sektor05/smartSwither/firmware/stm32cube/smartSwitcher/Core/Src/tim.c

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
/* Includes ------------------------------------------------------------------*/
#include "tim.h"

TIM_HandleTypeDef htim1;
TIM_HandleTypeDef htim2;
TIM_HandleTypeDef htim3;
TIM_HandleTypeDef htim4;

/* TIM1 init function */
void MX_TIM1_Init(void)
{

  TIM_ClockConfigTypeDef sClockSourceConfig = {0};
  TIM_MasterConfigTypeDef sMasterConfig = {0};

  htim1.Instance = TIM1;
  htim1.Init.Prescaler = 9;
  htim1.Init.CounterMode = TIM_COUNTERMODE_UP;
  htim1.Init.Period = 39;
  htim1.Init.ClockDivision = TIM_CLOCKDIVISION_DIV1;
  htim1.Init.RepetitionCounter = 0;
  htim1.Init.AutoReloadPreload = TIM_AUTORELOAD_PRELOAD_DISABLE;
  if (HAL_TIM_Base_Init(&htim1) != HAL_OK)
  {
    Error_Handler();
  }
  sClockSourceConfig.ClockSource = TIM_CLOCKSOURCE_INTERNAL;
  if (HAL_TIM_ConfigClockSource(&htim1, &sClockSourceConfig) != HAL_OK)
  {
    Error_Handler();
  }
  sMasterConfig.MasterOutputTrigger = TIM_TRGO_RESET;
  sMasterConfig.MasterSlaveMode = TIM_MASTERSLAVEMODE_DISABLE;
  if (HAL_TIMEx_MasterConfigSynchronization(&htim1, &sMasterConfig) != HAL_OK)
  {
    Error_Handler();
  }
}
/* TIM2 init function */
void MX_TIM2_Init(void)
{

  TIM_ClockConfigTypeDef sClockSourceConfig = {0};
  TIM_MasterConfigTypeDef sMasterConfig = {0};

  htim2.Instance = TIM2;
  htim2.Init.Prescaler = 9999;
  htim2.Init.CounterMode = TIM_COUNTERMODE_UP;
  htim2.Init.Period = 999;
  htim2.Init.ClockDivision = TIM_CLOCKDIVISION_DIV1;
  htim2.Init.AutoReloadPreload = TIM_AUTORELOAD_PRELOAD_DISABLE;
  if (HAL_TIM_Base_Init(&htim2) != HAL_OK)
  {
    Error_Handler();
  }
  sClockSourceConfig.ClockSource = TIM_CLOCKSOURCE_INTERNAL;
  if (HAL_TIM_ConfigClockSource(&htim2, &sClockSourceConfig) != HAL_OK)
  {
    Error_Handler();
  }
  sMasterConfig.MasterOutputTrigger = TIM_TRGO_RESET;
  sMasterConfig.MasterSlaveMode = TIM_MASTERSLAVEMODE_DISABLE;
  if (HAL_TIMEx_MasterConfigSynchronization(&htim2, &sMasterConfig) != HAL_OK)
  {
    Error_Handler();
  }
}
/* TIM3 init function */
void MX_TIM3_Init(void)
{

  TIM_ClockConfigTypeDef sClockSourceConfig = {0};
  TIM_MasterConfigTypeDef sMasterConfig = {0};

  htim3.Instance = TIM3;
  htim3.Init.Prescaler = 9999;
  htim3.Init.CounterMode = TIM_COUNTERMODE_UP;
  htim3.Init.Period = 999;
  htim3.Init.ClockDivision = TIM_CLOCKDIVISION_DIV1;
  htim3.Init.AutoReloadPreload = TIM_AUTORELOAD_PRELOAD_DISABLE;
  if (HAL_TIM_Base_Init(&htim3) != HAL_OK)
  {
    Error_Handler();
  }
  sClockSourceConfig.ClockSource = TIM_CLOCKSOURCE_INTERNAL;
  if (HAL_TIM_ConfigClockSource(&htim3, &sClockSourceConfig) != HAL_OK)
  {
    Error_Handler();
  }
  sMasterConfig.MasterOutputTrigger = TIM_TRGO_RESET;
  sMasterConfig.MasterSlaveMode = TIM_MASTERSLAVEMODE_DISABLE;
  if (HAL_TIMEx_MasterConfigSynchronization(&htim3, &sMasterConfig) != HAL_OK)
  {
    Error_Handler();
  }
}
/* TIM4 init function */
void MX_TIM4_Init(void)
{

  TIM_ClockConfigTypeDef sClockSourceConfig = {0};
  TIM_MasterConfigTypeDef sMasterConfig = {0};

  htim4.Instance = TIM4;
  htim4.Init.Prescaler = 9999;
  htim4.Init.CounterMode = TIM_COUNTERMODE_UP;
  htim4.Init.Period = 3000;
  htim4.Init.ClockDivision = TIM_CLOCKDIVISION_DIV1;
  htim4.Init.AutoReloadPreload = TIM_AUTORELOAD_PRELOAD_DISABLE;
  if (HAL_TIM_Base_Init(&htim4) != HAL_OK)
  {
    Error_Handler();
  }
  sClockSourceConfig.ClockSource = TIM_CLOCKSOURCE_INTERNAL;
  if (HAL_TIM_ConfigClockSource(&htim4, &sClockSourceConfig) != HAL_OK)
  {
    Error_Handler();
  }
  sMasterConfig.MasterOutputTrigger = TIM_TRGO_RESET;
  sMasterConfig.MasterSlaveMode = TIM_MASTERSLAVEMODE_DISABLE;
  if (HAL_TIMEx_MasterConfigSynchronization(&htim4, &sMasterConfig) != HAL_OK)
  {
    Error_Handler();
  }
}

void HAL_TIM_Base_MspInit(TIM_HandleTypeDef* tim_baseHandle)
{

  if(tim_baseHandle->Instance==TIM1)
  {
    /* TIM1 clock enable */
    __HAL_RCC_TIM1_CLK_ENABLE();

    /* TIM1 interrupt Init */
    HAL_NVIC_SetPriority(TIM1_BRK_IRQn, 0, 0);
    HAL_NVIC_EnableIRQ(TIM1_BRK_IRQn);
  }
  else if(tim_baseHandle->Instance==TIM2)
  {
    /* TIM2 clock enable */
    __HAL_RCC_TIM2_CLK_ENABLE();

    /* TIM2 interrupt Init */
    HAL_NVIC_SetPriority(TIM2_IRQn, 2, 0);
    HAL_NVIC_EnableIRQ(TIM2_IRQn);
  }
  else if(tim_baseHandle->Instance==TIM3)
  {
    /* TIM3 clock enable */
    __HAL_RCC_TIM3_CLK_ENABLE();

    /* TIM3 interrupt Init */
    HAL_NVIC_SetPriority(TIM3_IRQn, 1, 0);
    HAL_NVIC_EnableIRQ(TIM3_IRQn);
  }
  else if(tim_baseHandle->Instance==TIM4)
  {
    /* TIM4 clock enable */
    __HAL_RCC_TIM4_CLK_ENABLE();

    /* TIM4 interrupt Init */
    HAL_NVIC_SetPriority(TIM4_IRQn, 1, 0);
    HAL_NVIC_EnableIRQ(TIM4_IRQn);
  }
}

void HAL_TIM_Base_MspDeInit(TIM_HandleTypeDef* tim_baseHandle)
{

  if(tim_baseHandle->Instance==TIM1)
  {
    /* Peripheral clock disable */
    __HAL_RCC_TIM1_CLK_DISABLE();

    /* TIM1 interrupt Deinit */
    HAL_NVIC_DisableIRQ(TIM1_BRK_IRQn);
  }
  else if(tim_baseHandle->Instance==TIM2)
  {
    /* Peripheral clock disable */
    __HAL_RCC_TIM2_CLK_DISABLE();

    /* TIM2 interrupt Deinit */
    HAL_NVIC_DisableIRQ(TIM2_IRQn);
  }
  else if(tim_baseHandle->Instance==TIM3)
  {
    /* Peripheral clock disable */
    __HAL_RCC_TIM3_CLK_DISABLE();

    /* TIM3 interrupt Deinit */
    HAL_NVIC_DisableIRQ(TIM3_IRQn);
  }
  else if(tim_baseHandle->Instance==TIM4)
  {
    /* Peripheral clock disable */
    __HAL_RCC_TIM4_CLK_DISABLE();

    /* TIM4 interrupt Deinit */
    HAL_NVIC_DisableIRQ(TIM4_IRQn);
  }
}

/* USER CODE BEGIN 1 */

void HAL_TIM_PeriodElapsedCallback(TIM_HandleTypeDef *htim)
{
    if(htim->Instance == TIM1){
      sendTempToCAN();
    }
    else if(htim->Instance == TIM2)
    {
    	LightControlDM1();
    }else if(htim->Instance == TIM3){
      LightControlDM2();
    }else if(htim->Instance == TIM4){ // таймер на 30 сек. отпавка темературы
      sendTempToCAN();
    }
  
}

void SetTimeTimer_Dim1(uint16_t time_seconds)
{
    // Рассчитываем значение перезагрузки (ARR) из времени в секундах
    // ARR = (T * F_CLK) / (PSC + 1) - 1
    uint32_t arr_value = ( (uint32_t)time_seconds * 10000000 ) / (9999 + 1) - 1;

    // Проверяем границы (ARR — 16-битный регистр, максимум 65535)
    if (arr_value > 65535) {
        arr_value = 65535;
    }

    // Останавливаем таймер перед изменением настроек
    HAL_TIM_Base_Stop_IT(&htim2);

    // Устанавливаем новое значение периода
    __HAL_TIM_SET_AUTORELOAD(&htim2, arr_value);

    // Сбрасываем счетчик
    __HAL_TIM_SET_COUNTER(&htim2, 0);

    // Перезапускаем таймер
    HAL_TIM_Base_Start_IT(&htim2);
}

void SetTimeTimer_Dim2(uint16_t time_seconds)
{
    // Рассчитываем значение перезагрузки (ARR) из времени в секундах
    // ARR = (T * F_CLK) / (PSC + 1) - 1
    uint32_t arr_value = ( (uint32_t)time_seconds * 10000000 ) / (9999 + 1) - 1;

    // Проверяем границы (ARR — 16-битный регистр, максимум 65535)
    if (arr_value > 65535) {
        arr_value = 65535;
    }

    // Останавливаем таймер перед изменением настроек
    HAL_TIM_Base_Stop_IT(&htim3);

    // Устанавливаем новое значение периода
    __HAL_TIM_SET_AUTORELOAD(&htim3, arr_value);

    // Сбрасываем счетчик
    __HAL_TIM_SET_COUNTER(&htim3, 0);

    // Перезапускаем таймер
    HAL_TIM_Base_Start_IT(&htim3);
}
/* USER CODE END 1 */
