sektor05/smartSwither/firmware/stm32cube/smartSwitcher/Core/Inc/adc.h

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
/* Define to prevent recursive inclusion -------------------------------------*/
#ifndef __ADC_H__
#define __ADC_H__

#ifdef __cplusplus
extern "C" {
#endif

/* Includes ------------------------------------------------------------------*/
#include "main.h"

extern ADC_HandleTypeDef hadc1;

/* USER CODE BEGIN Private defines */
enum{
	CHANALS_ADC = 3,
	CHANAL_ADC_TEMP =0,
	CHANAL_ADC_TMPCHIP =1,
	CHANAL_ADC_VREF =2,
	ADC_MAX_VAL=4094
};

#define KOF_RC_FILTR 10
/* USER CODE END Private defines */

void MX_ADC1_Init(void);

/* USER CODE BEGIN Prototypes */
typedef struct AdcValues{
	uint16_t adcChanal[CHANALS_ADC]; //0-3 pin 4 temp 5 vref
	uint16_t FadcChanal;
	uint16_t TEMP;
}adcval_t;
extern adcval_t Adc;

void HAL_ADC_ConvCpltCallback(ADC_HandleTypeDef* hadc);
uint16_t FiltrRC1(uint16_t data);
double readTemperatureLM335(uint16_t data);
/* USER CODE END Prototypes */

#ifdef __cplusplus
}
#endif

#endif /* __ADC_H__ */
